GhadeerElmkaiel/Laser-Keyboard/Designs and files/3D printing files/Keyboard parts/lower_base.stl

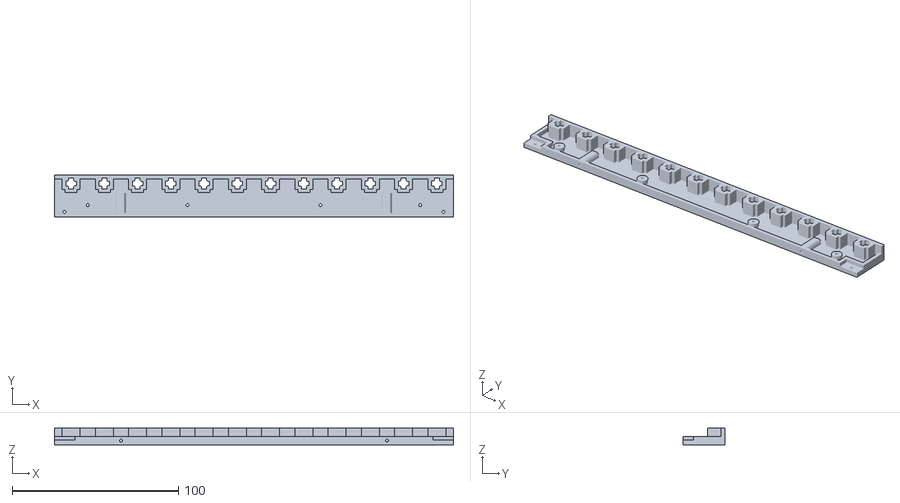
[picture p16: CAD file, 2025-08-03]
Designs and files/3D printing files/Keyboard parts/lower_base.stl
240.0 x 25.0 x 10.0
