GhadeerElmkaiel/Laser-Keyboard/Designs and files/3D printing files/Testing/Laser_testing_laser_hoder.stl

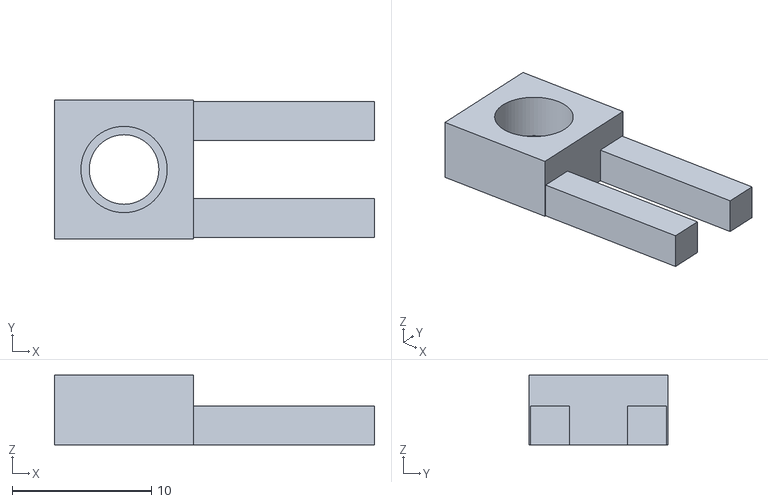
[picture p17: CAD file, 2025-08-03]
Designs and files/3D printing files/Testing/Laser_testing_laser_hoder.stl
23.0 x 10.0 x 5.00
