GhadeerElmkaiel/Laser-Keyboard/Designs and files/3D printing files/Keyboard parts/laser_side_base.stl

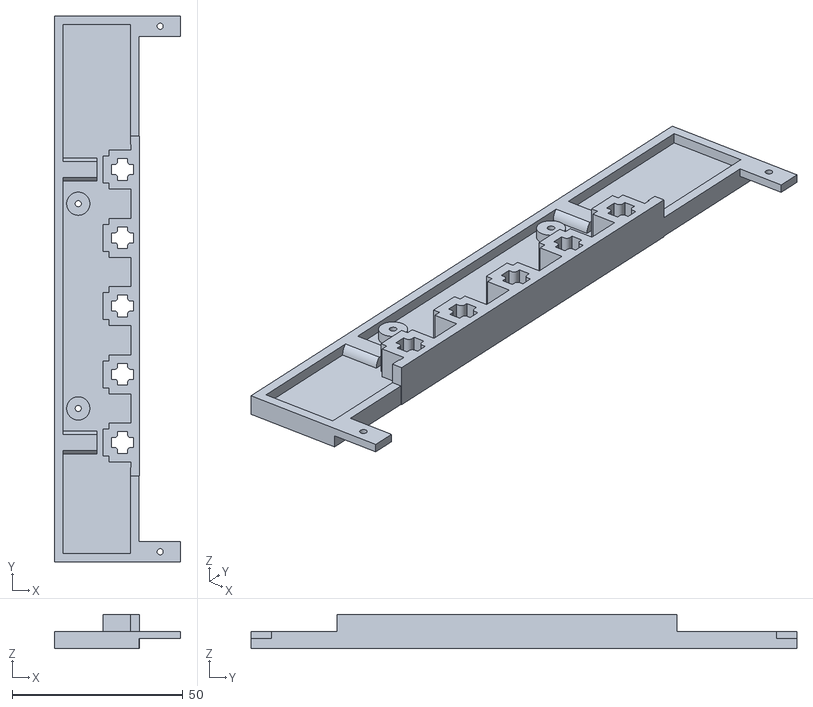
[picture p18: CAD file, 2025-08-03]
Designs and files/3D printing files/Keyboard parts/laser_side_base.stl
37.0 x 160.0 x 10.0
