GhadeerElmkaiel/Laser-Keyboard/Designs and files/3D printing files/Testing/Laser_slider_base v1.stl

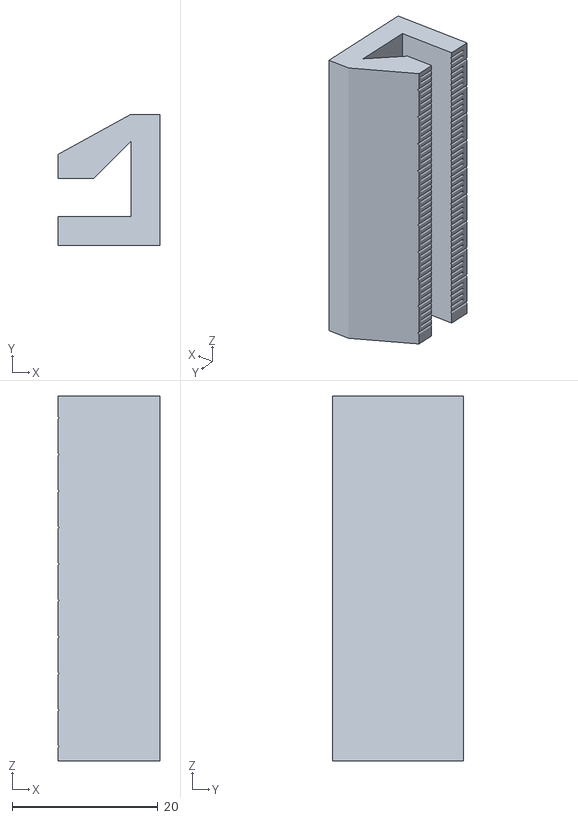
[picture p19: CAD file, 2025-08-03]
Designs and files/3D printing files/Testing/Laser_slider_base v1.stl
14.0 x 18.0 x 50.0
