GhadeerElmkaiel/Laser-Keyboard/Designs and files/3D printing files/Keyboard parts/side_wall_L.stl

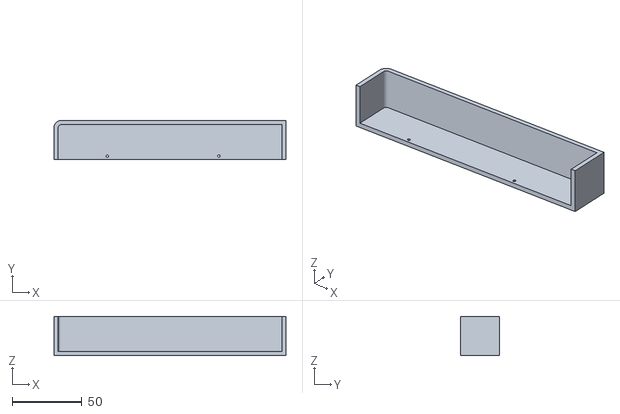
[picture p20: CAD file, 2025-08-03]
Designs and files/3D printing files/Keyboard parts/side_wall_L.stl
166.4 x 28.0 x 28.2
