GhadeerElmkaiel/Laser-Keyboard/Designs and files/3D printing files/Testing/laser_hall_test v1.stl

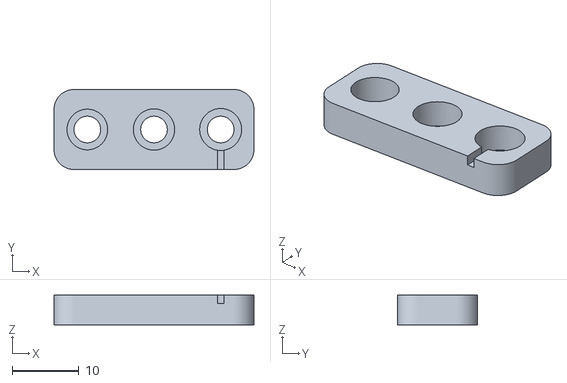
[picture p21: CAD file, 2025-08-03]
Designs and files/3D printing files/Testing/laser_hall_test v1.stl
30.0 x 12.0 x 4.50
