GhadeerElmkaiel/Laser-Keyboard/Designs and files/3D printing files/Keyboard parts/bottom_laser_cover.stl

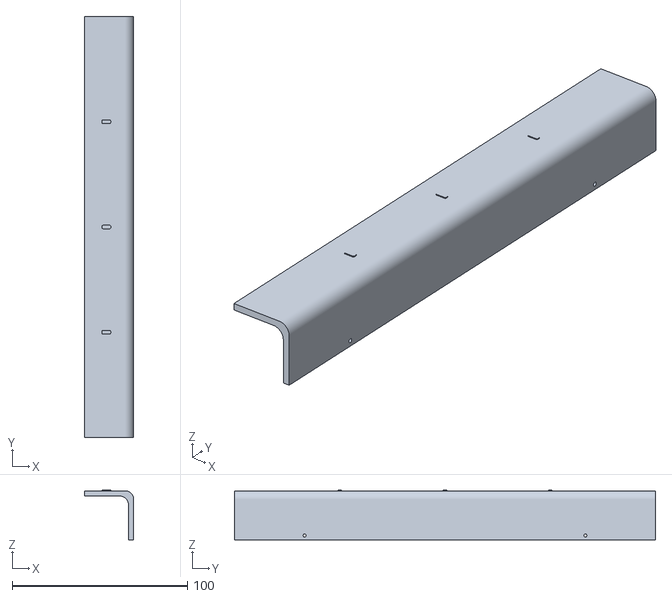
[picture p22: CAD file, 2025-08-03]
Designs and files/3D printing files/Keyboard parts/bottom_laser_cover.stl
28.2 x 240.0 x 28.4
