GhadeerElmkaiel/Laser-Keyboard/Designs and files/3D printing files/Testing/3x3_KB_test.stl

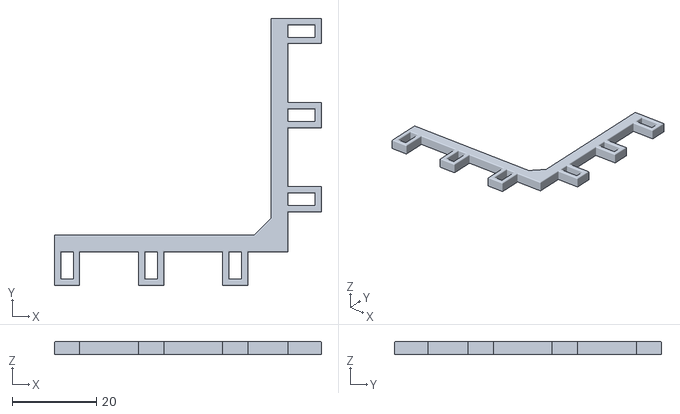
[picture p23: CAD file, 2025-08-03]
Designs and files/3D printing files/Testing/3x3_KB_test.stl
63.5 x 63.5 x 3.20
