GhadeerElmkaiel/Laser-Keyboard/Designs and files/3D printing files/Keyboard parts/top_wall.stl

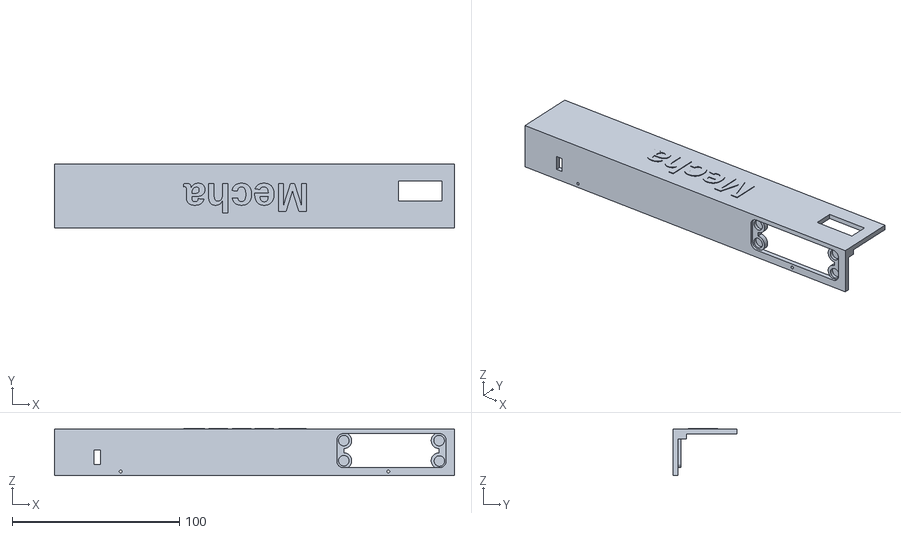
[picture p24: CAD file, 2025-08-03]
Designs and files/3D printing files/Keyboard parts/top_wall.stl
239.2 x 38.0 x 28.4
